logimic/iqrfboard/documents/examples-docs/example-GY-49/README.md

# Ambient Light sensor

[Datasheet](https://datasheets.maximintegrated.com/en/ds/MAX44009.pdf)
