logimic/iqrfboard/docs/assets/images/iqrfboardconnectsensors-2-800x600.png

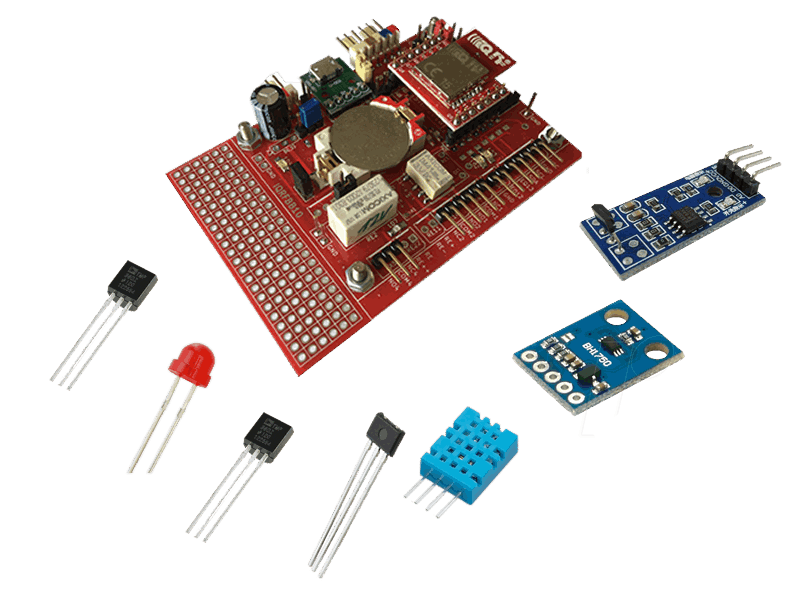
docs/assets/images/iqrfboardconnectsensors-2-800x600.png
