logimic/iqrfboard/docs/assets/images/iqrfboardkit-800x600.png

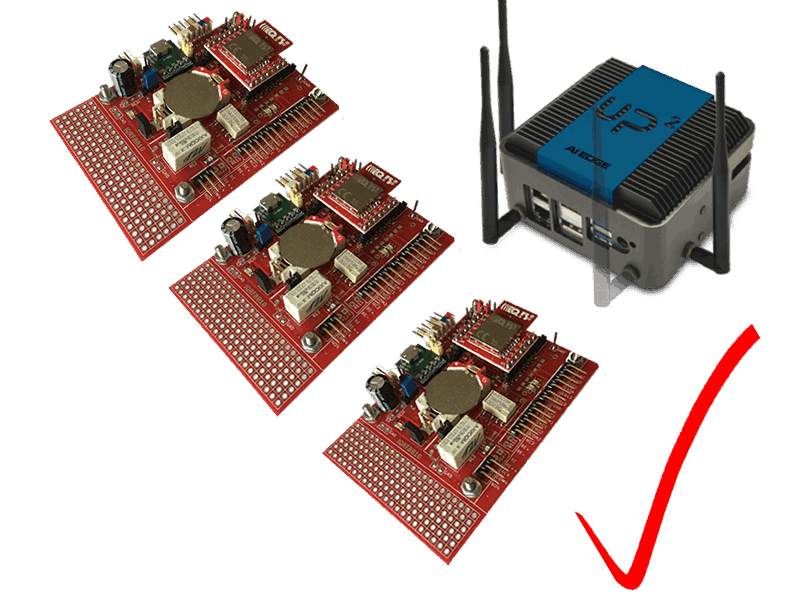
docs/assets/images/iqrfboardkit-800x600.png
