logimic/iqrfboard/docs/assets/images/iqrfboardloadsoftware-5-800x600.png

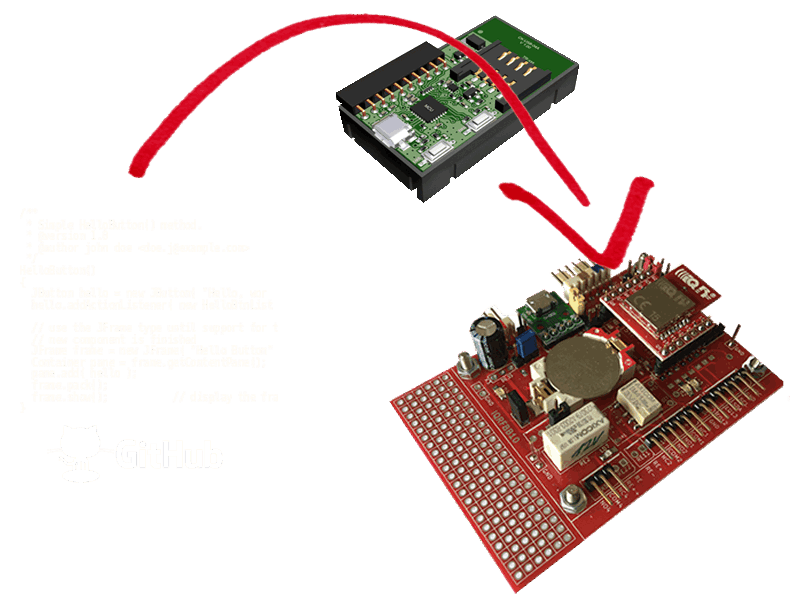
docs/assets/images/iqrfboardloadsoftware-5-800x600.png
