logimic/iqrfboard/docs/assets/images/iqrfboardsystem2-2-800x600.png

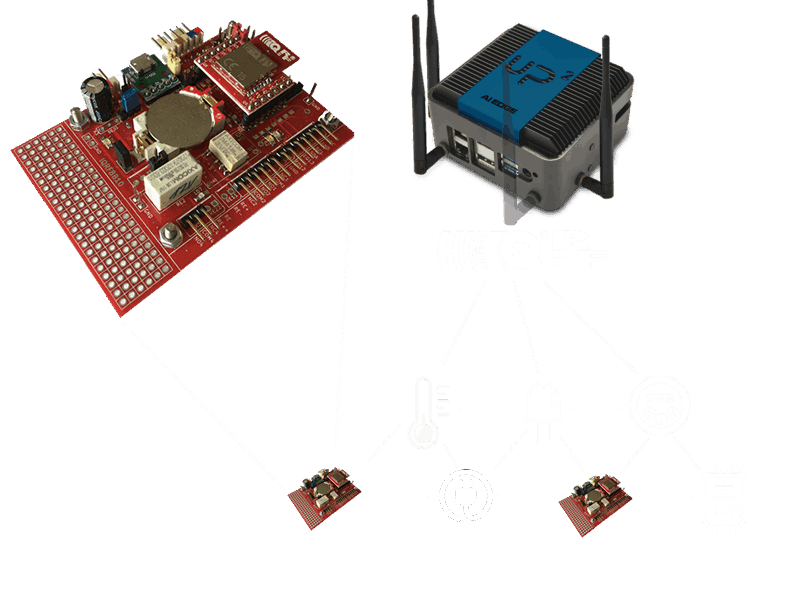
docs/assets/images/iqrfboardsystem2-2-800x600.png
