logimic/iqrfboard/docs/assets/images/iqrfboardsystem2-800x600.png

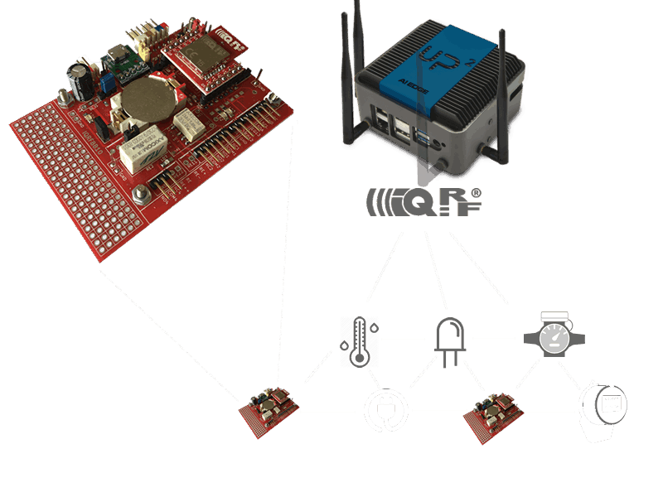
docs/assets/images/iqrfboardsystem2-800x600.png
