logimic/iqrfboard/docs/assets/images/iqrfboardtoproduct-800x600.png

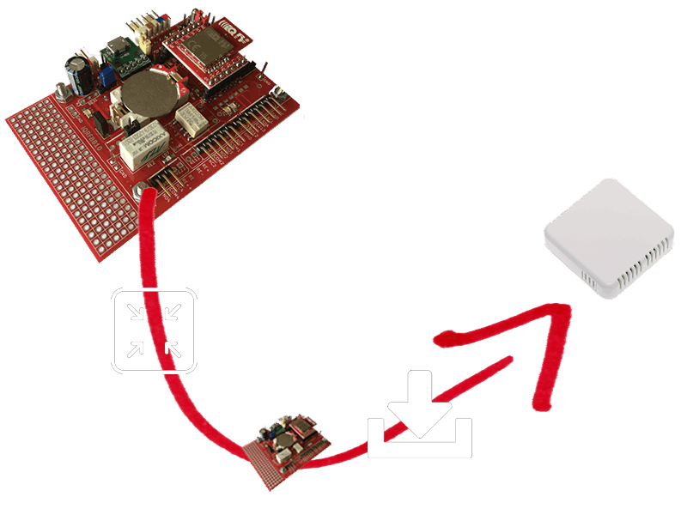
docs/assets/images/iqrfboardtoproduct-800x600.png
