logimic/iqrfboard/docs/book/examples-docs/dpa-epir/epir.png

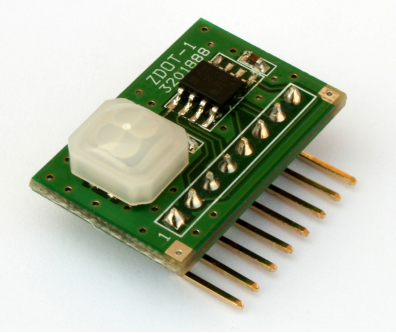
docs/book/examples-docs/dpa-epir/epir.png
