logimic/iqrfboard/docs/book/examples-docs/dpa-hall/hall.png

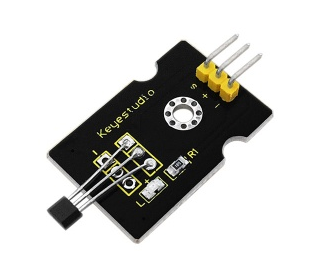
docs/book/examples-docs/dpa-hall/hall.png
