logimic/iqrfboard/docs/book/examples-docs/dpa-htu21d/dpa-htu21d.jpg

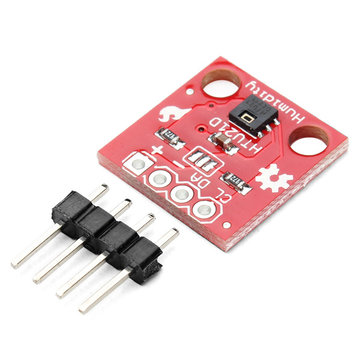
docs/book/examples-docs/dpa-htu21d/dpa-htu21d.jpg
