logimic/iqrfboard/docs/book/examples-docs/example-GY-49/GY49.jpg

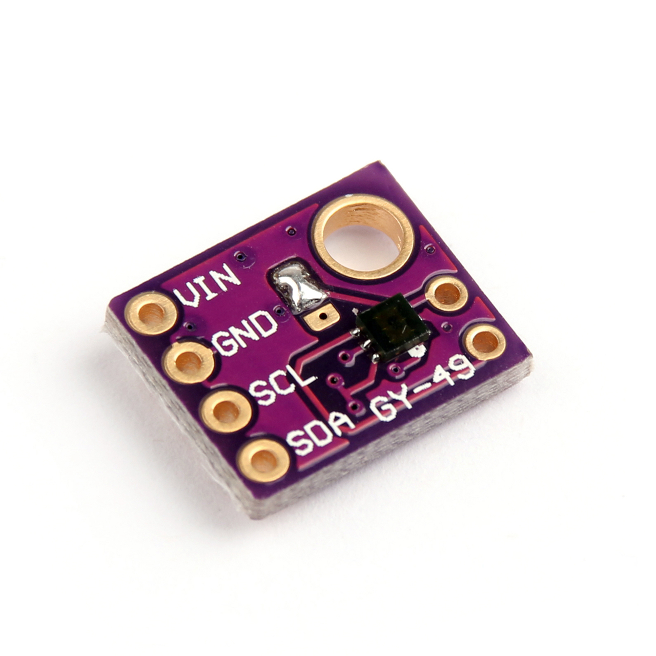
docs/book/examples-docs/example-GY-49/GY49.jpg
