logimic/iqrfboard/docs/book/examples-docs/example-GY-BME280/GY-BME280.jpg

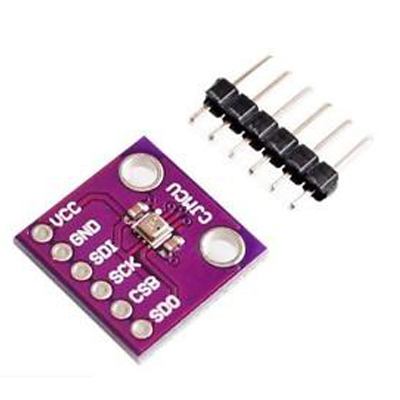
docs/book/examples-docs/example-GY-BME280/GY-BME280.jpg
