logimic/iqrfboard/docs/book/examples-docs/standard-photorezistor/photorezistor.png

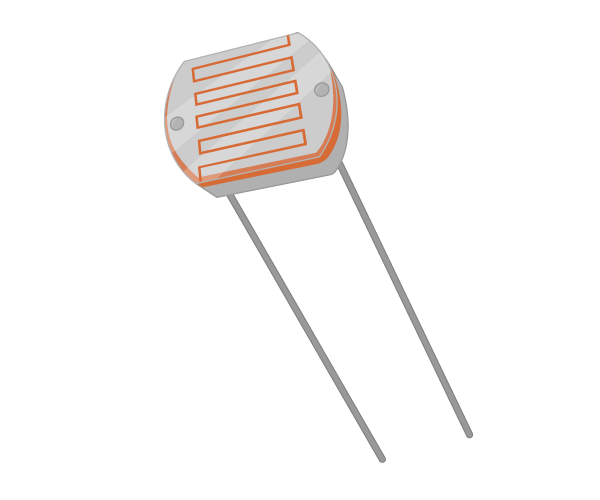
docs/book/examples-docs/standard-photorezistor/photorezistor.png
