logimic/iqrfboard/docs/book/examples-docs/standard-thermistor/thermistor.png

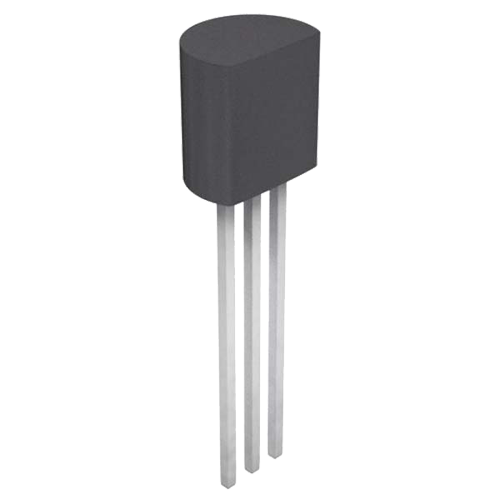
docs/book/examples-docs/standard-thermistor/thermistor.png
