logimic/iqrfboard/documents/files/images/ds-start-04-case.jpg

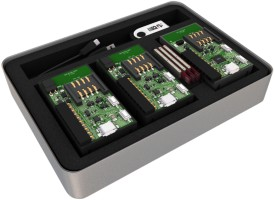
documents/files/images/ds-start-04-case.jpg
