logimic/iqrfboard/documents/files/images/example_small.png

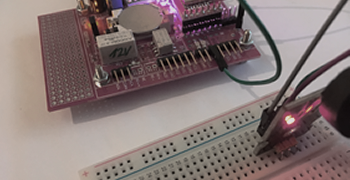
documents/files/images/example_small.png
