logimic/iqrfboard/documents/files/images/github.png

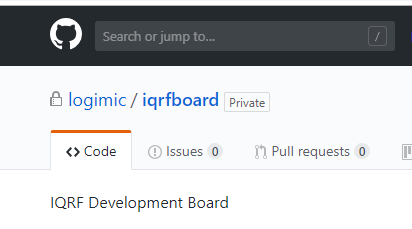
documents/files/images/github.png
