logimic/iqrfboard/documents/files/images/hwDesign_small.png

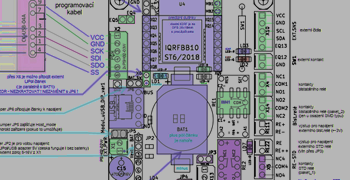
documents/files/images/hwDesign_small.png
