logimic/iqrfboard/documents/files/images/IMG_1103.JPG

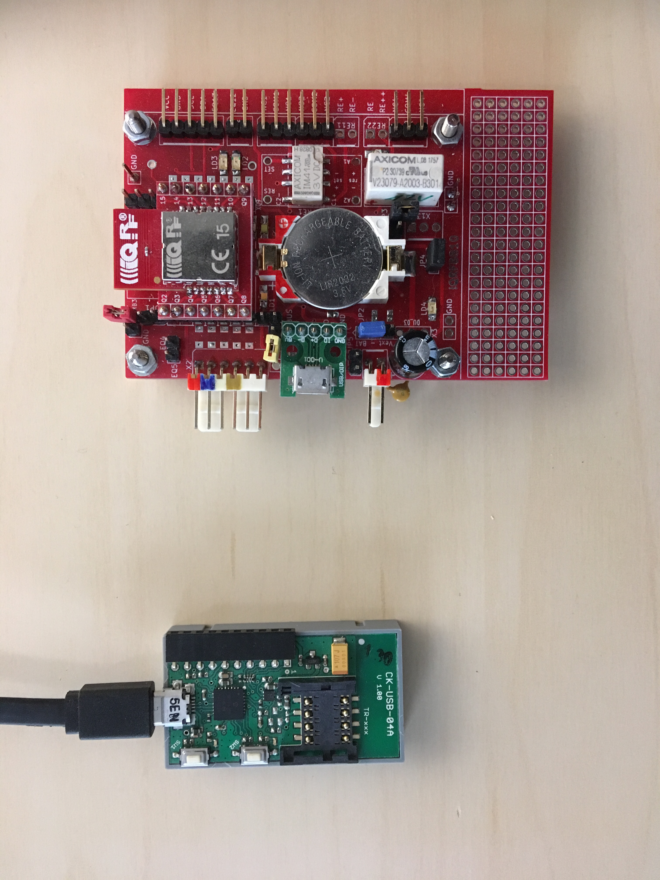
documents/files/images/IMG_1103.JPG
