logimic/iqrfboard/documents/files/images/iqrfboard-1710x1524.png

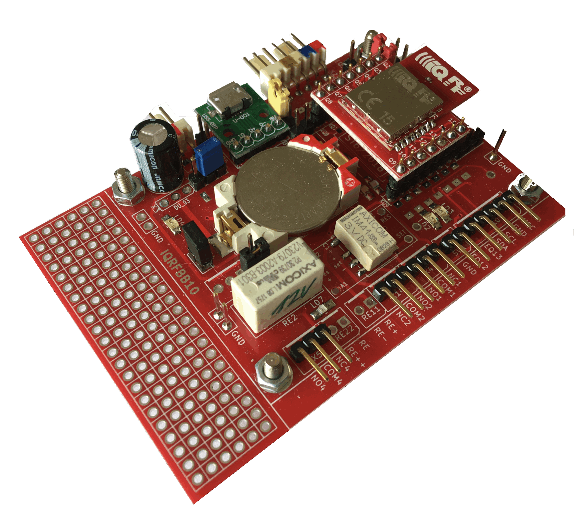
documents/files/images/iqrfboard-1710x1524.png
