logimic/iqrfboard/documents/files/images/iqrfboard.png

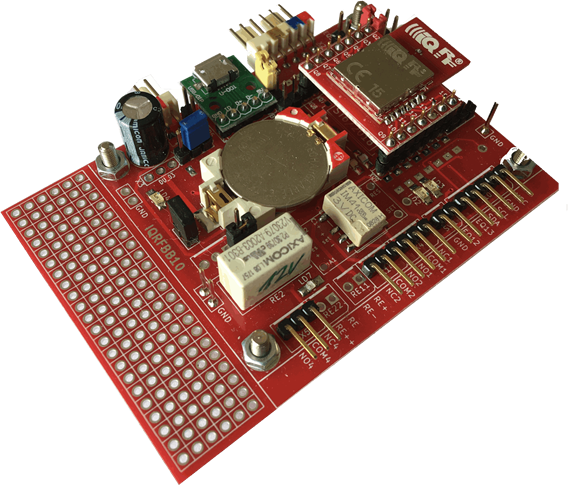
documents/files/images/iqrfboard.png
