logimic/iqrfboard/documents/files/images/tr-76da-dimensions.jpg

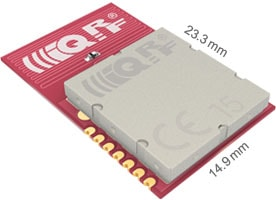
documents/files/images/tr-76da-dimensions.jpg
