logimic/iqrfboard/documents/files/images/allParts_small.png

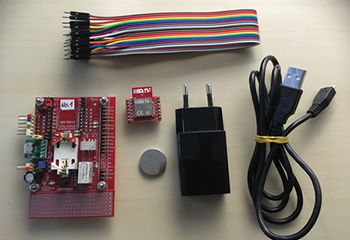
documents/files/images/allParts_small.png
